Dieu-de-l-elec/Pocket-Dice/assets/PCB 3 3d.png

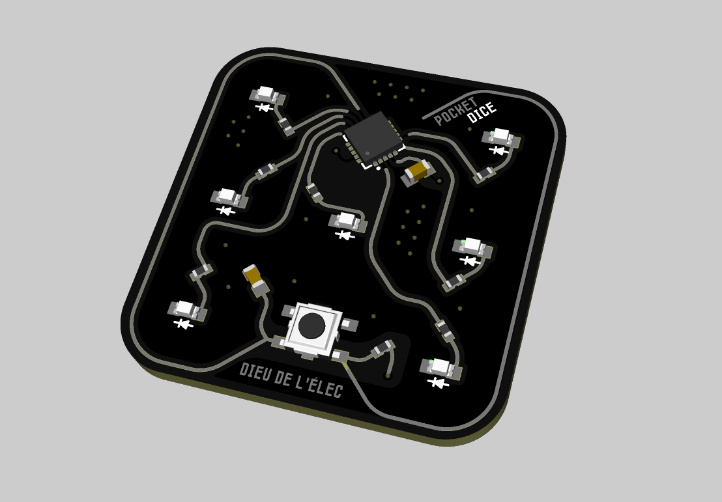
assets/PCB 3 3d.png
