Dieu-de-l-elec/Pocket-Dice/assets/PCB 3 back 3d.png

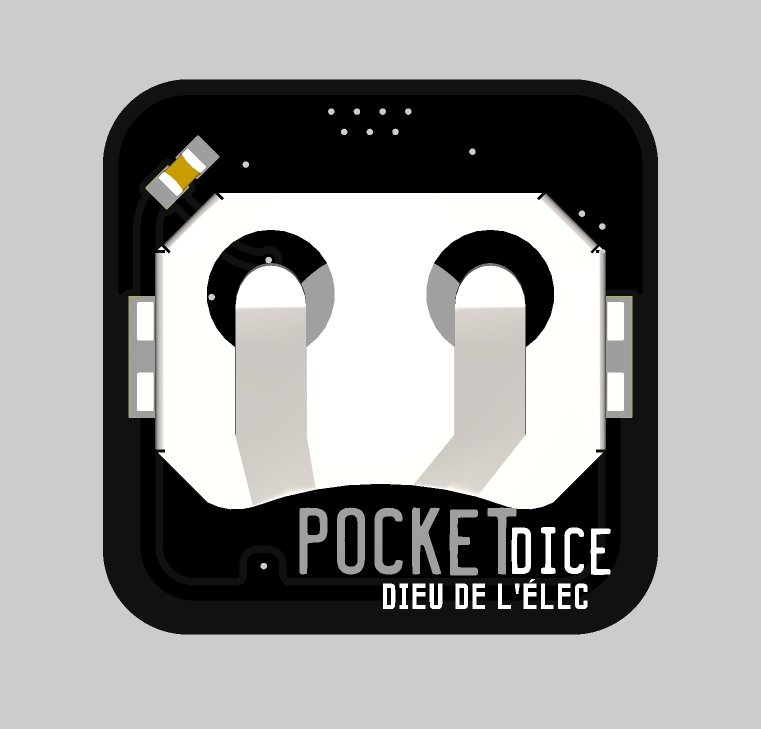
assets/PCB 3 back 3d.png
