Dieu-de-l-elec/Pocket-Dice/assets/PCB 3d render 1.png

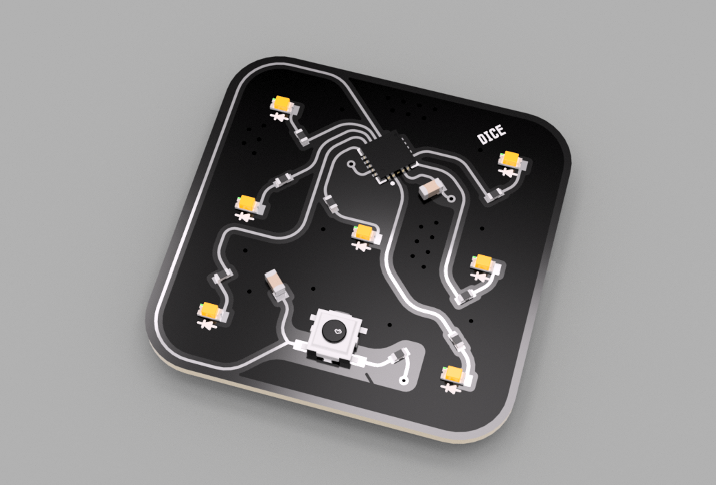
assets/PCB 3d render 1.png
