Dieu-de-l-elec/Pocket-Dice/assets/PCB 3d render 2.png

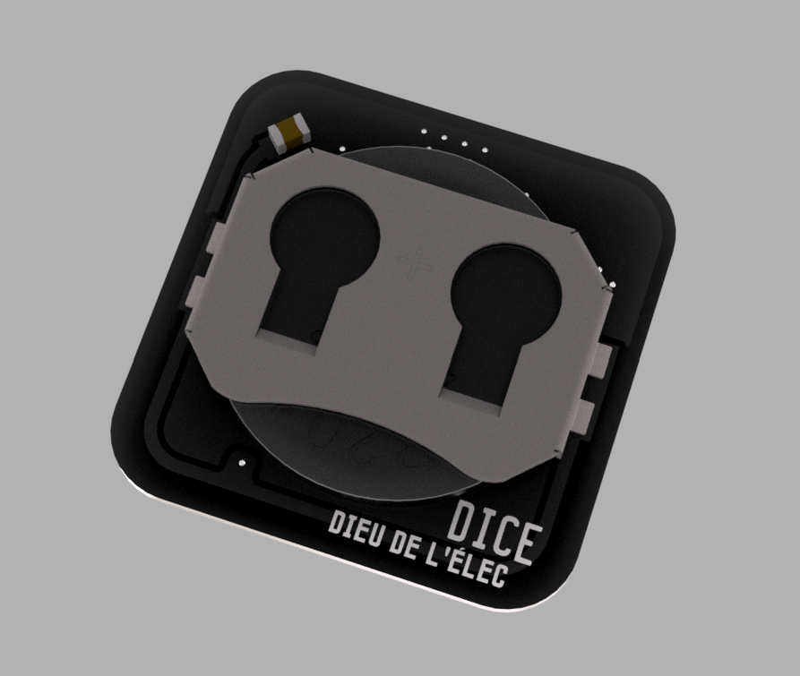
assets/PCB 3d render 2.png
