Dieu-de-l-elec/Pocket-Dice/assets/PCB 3d render 3.png

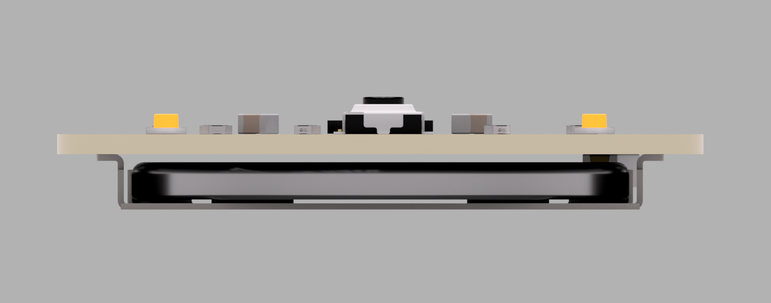
assets/PCB 3d render 3.png
