Dieu-de-l-elec/Pocket-Dice/assets/PCB 4.png

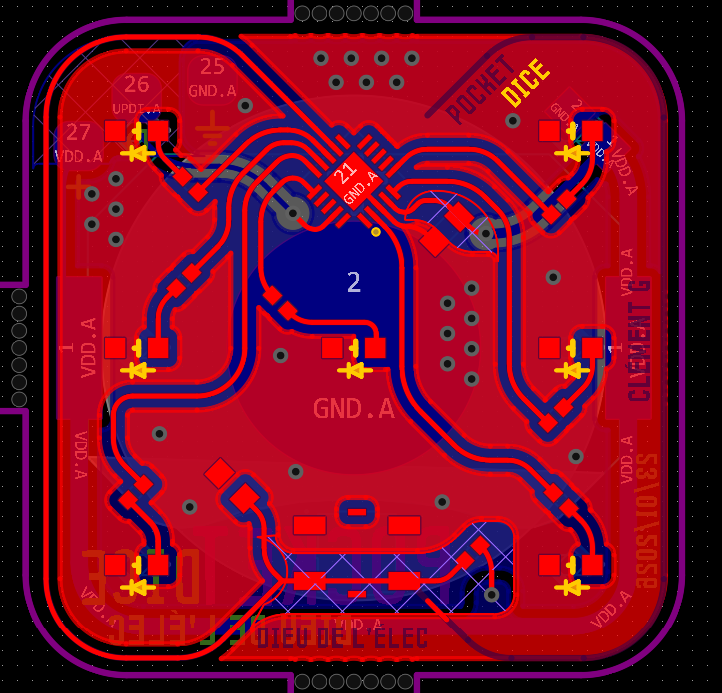
assets/PCB 4.png
