Dieu-de-l-elec/Pocket-Dice/assets/RENDER 1.png

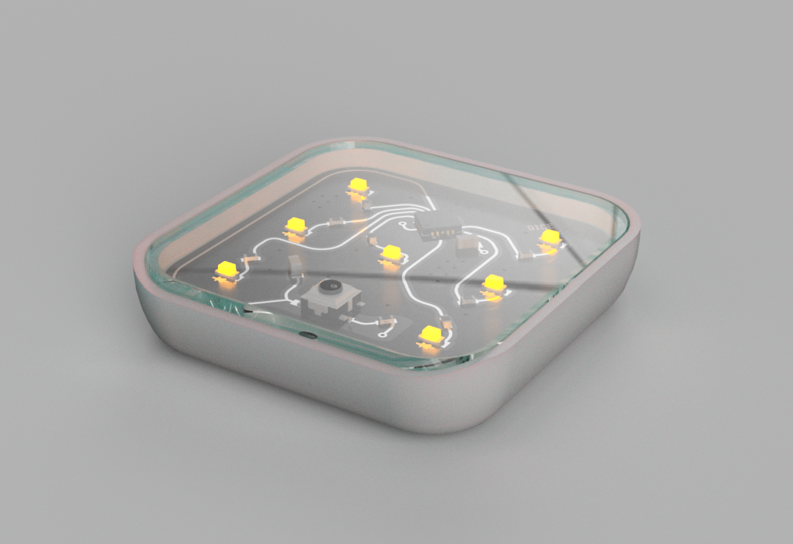
assets/RENDER 1.png
