Dieu-de-l-elec/Pocket-Dice/assets/RENDER 4.png

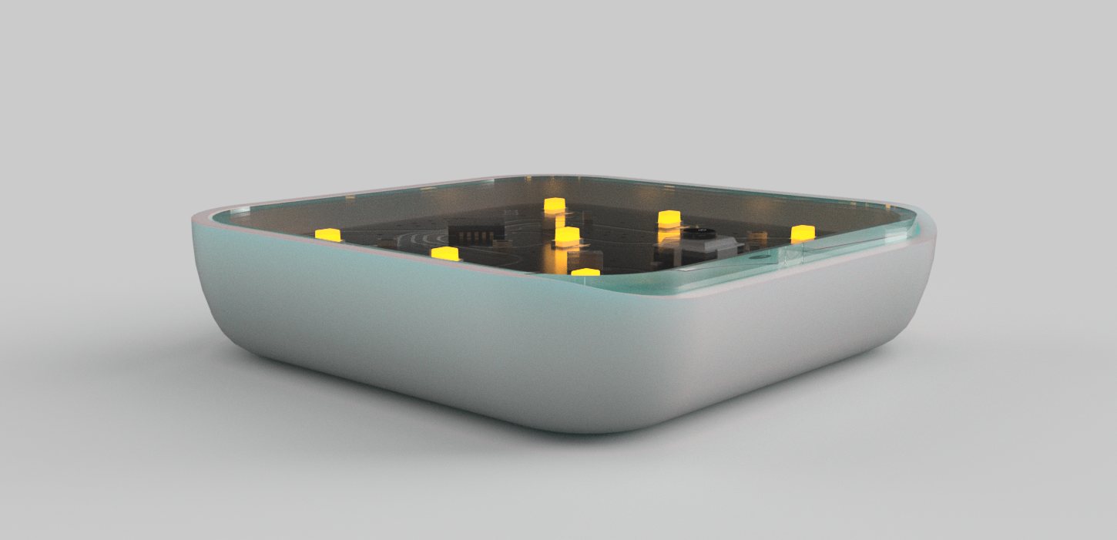
assets/RENDER 4.png
