Dieu-de-l-elec/Pocket-Dice/assets/RENDER 6.png

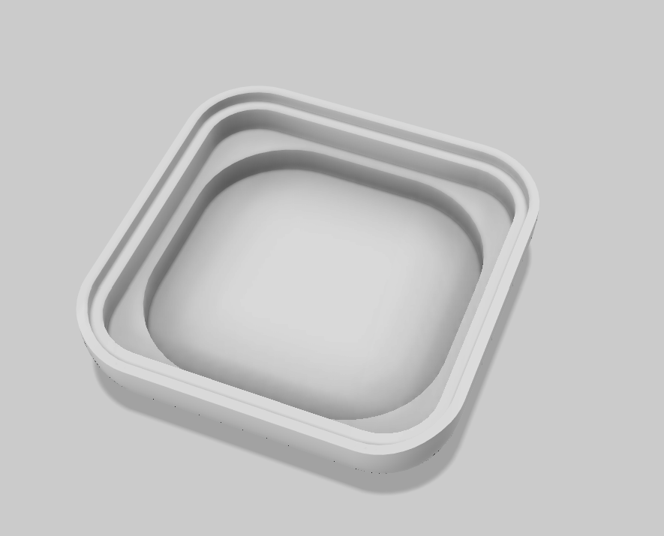
assets/RENDER 6.png
