Dieu-de-l-elec/Pocket-Dice/assets/UPDI.png

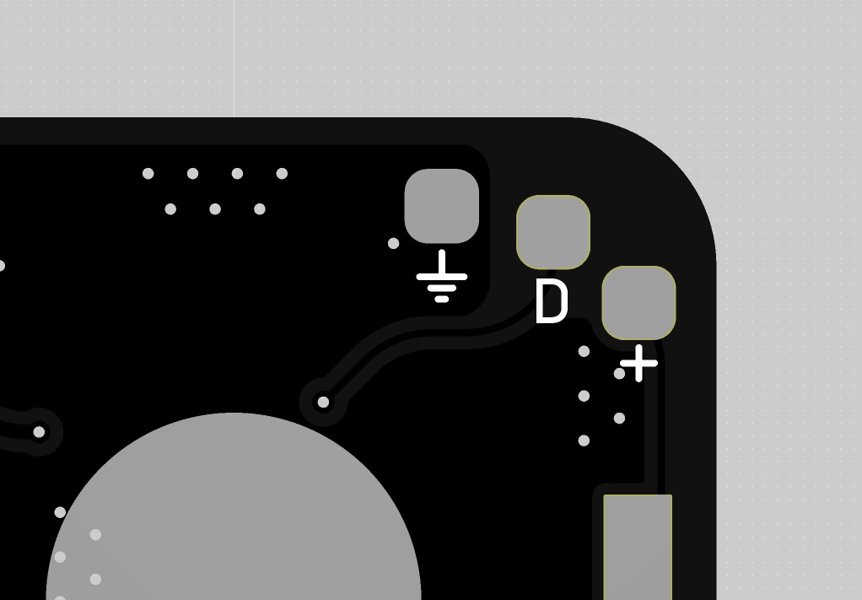
assets/UPDI.png
