Dieu-de-l-elec/Pocket-Dice/PCB/PCB PANEL 2D n.png

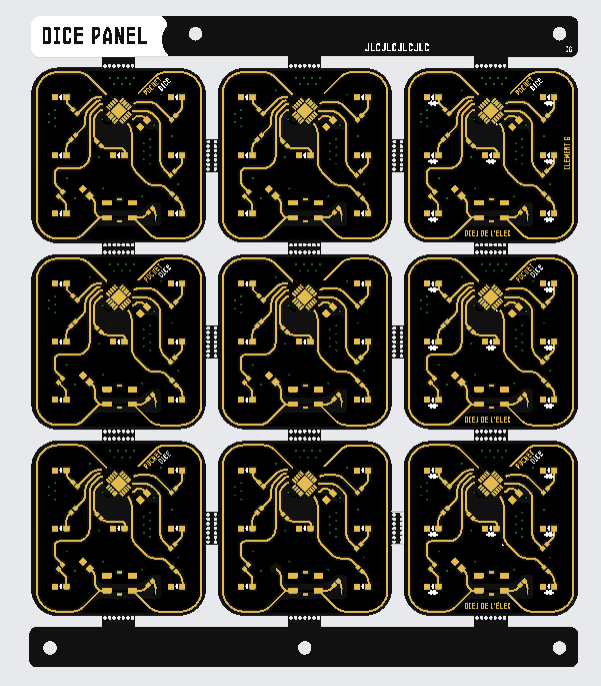
PCB/PCB PANEL 2D n.png
