Dieu-de-l-elec/Pocket-Dice/PCB/PCB PANEL back.png

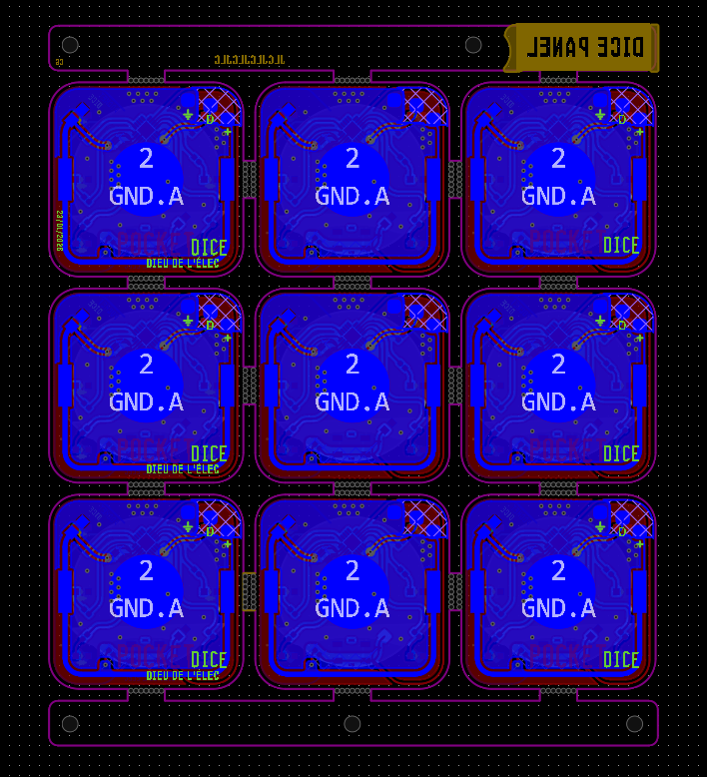
PCB/PCB PANEL back.png
