Dieu-de-l-elec/Pocket-Dice/PCB/PCB PANEL.png

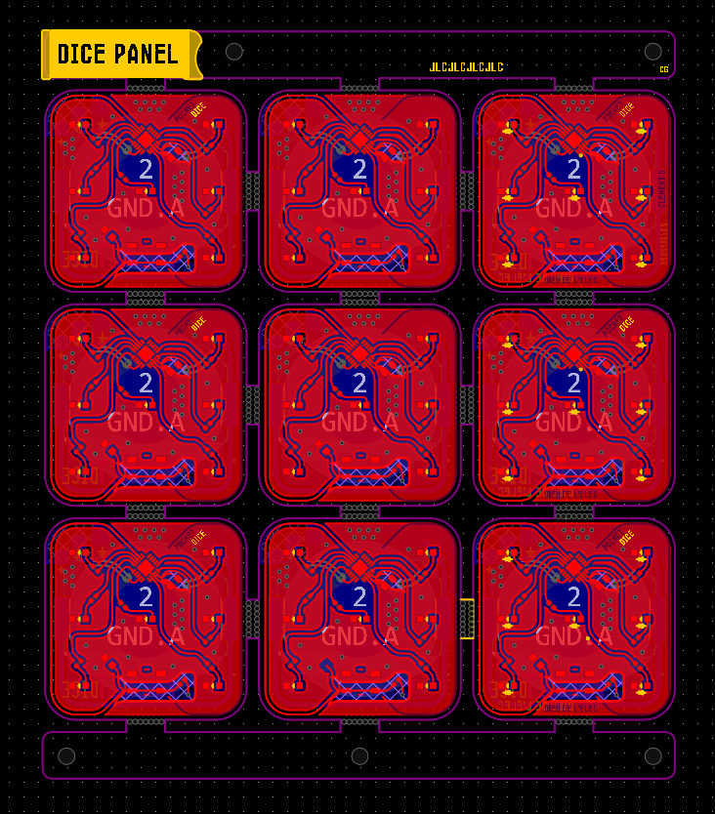
PCB/PCB PANEL.png
